mhamzalimanlar/WIFI_HOME_SECURITY_SYS_V01/Project_Libraries/Steps/LM2675M-12.STEP

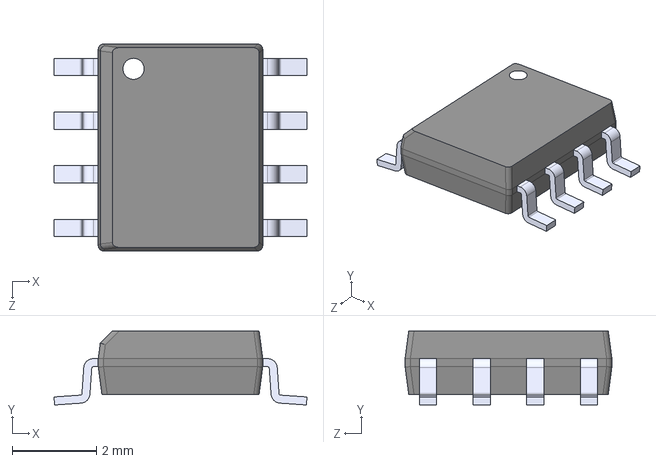
[picture p16: CAD file, 2023-01-26]
Project_Libraries/Steps/LM2675M-12.STEP
5.99 x 1.75 x 4.90 mm
