mhamzalimanlar/WIFI_HOME_SECURITY_SYS_V01/Project_Libraries/Steps/Library-SOT23F-1.STEP

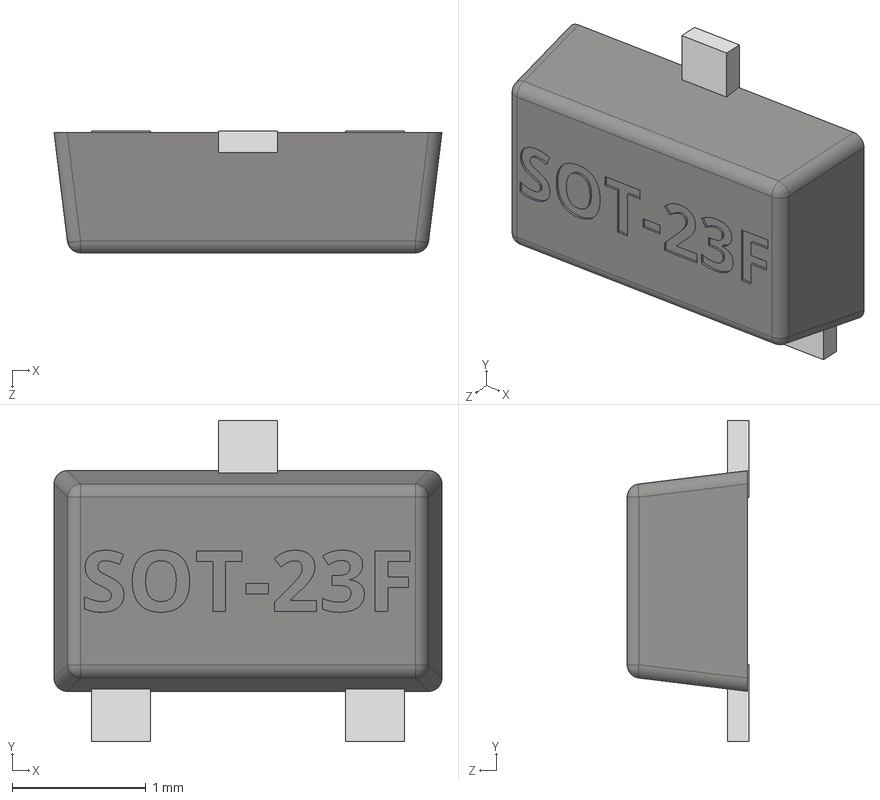
[picture p17: CAD file, 2023-01-26]
Project_Libraries/Steps/Library-SOT23F-1.STEP
2.90 x 2.40 x 0.91 mm
Pin_3
Cap
Pin_1
Pin_2
