mhamzalimanlar/WIFI_HOME_SECURITY_SYS_V01/Project_Libraries/Steps/CAPC0603.STEP

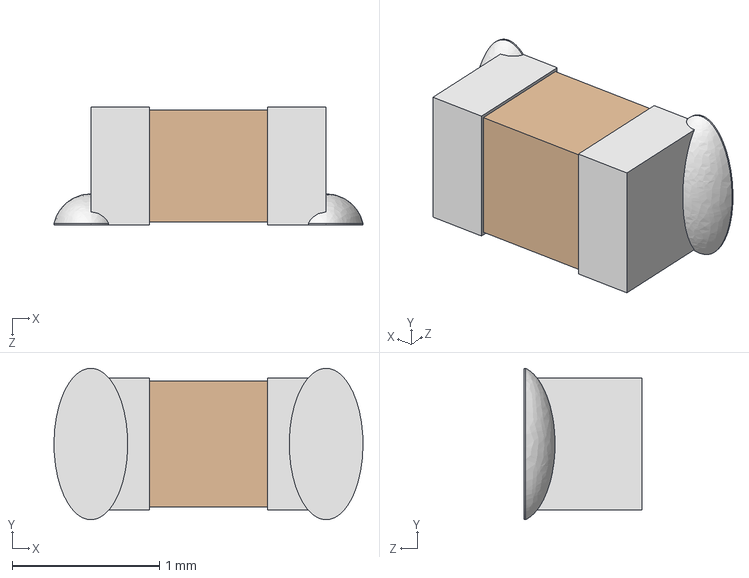
[picture p18: CAD file, 2023-01-26]
Project_Libraries/Steps/CAPC0603.STEP
2.10 x 1.03 x 0.8 mm
