mhamzalimanlar/WIFI_HOME_SECURITY_SYS_V01/Project_Libraries/Steps/Library-Hahn BV EI 302 2902.step

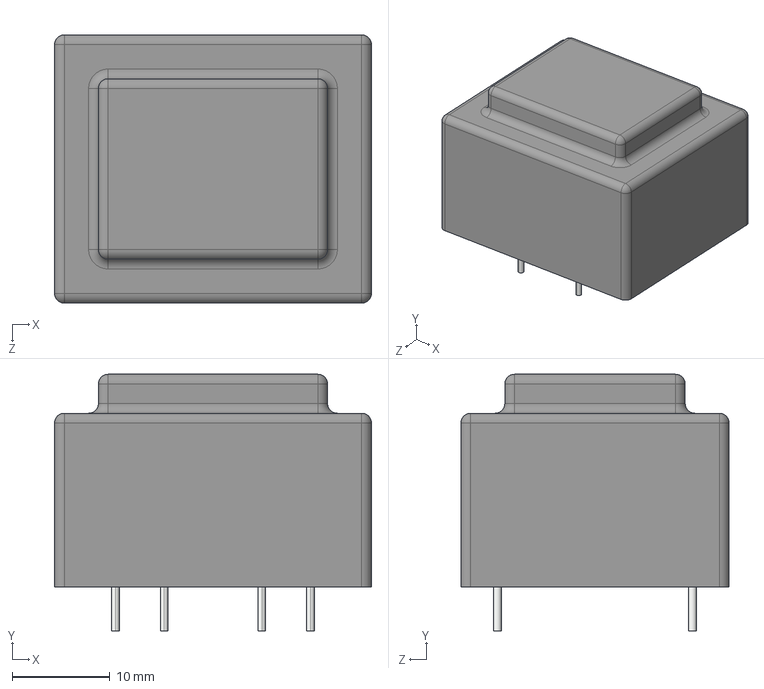
[picture p19: CAD file, 2023-01-26]
Project_Libraries/Steps/Library-Hahn BV EI 302 2902.step
32.5 x 26.3 x 27.5 mm
