mhamzalimanlar/WIFI_HOME_SECURITY_SYS_V01/Project_Libraries/Steps/STM32 LQFP48.step

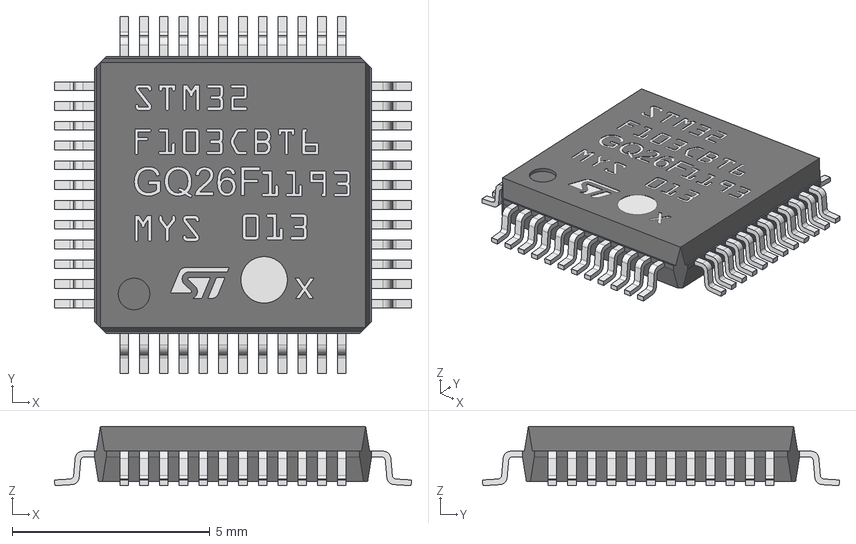
[picture p20: CAD file, 2023-01-26]
Project_Libraries/Steps/STM32 LQFP48.step
9.02 x 9.02 x 1.50 mm
